ji2tab/OpenCCVoice/CCVoice_2_24f/NOTES_FOR_UPGRADE.md

# アップグレードガイド — OpenCCVoice

--------------------------------------------------------------------

## v2.24 → v2.24f アップグレード

**スケッチの差し替えのみで完了します。**

- `V`（バージョン確認）と `Z`（ソフトウェアリセット）コマンドの追加のみです。
- EEPROM CONFIG_VERSION = 6（変更なし）。`F` コマンド不要。

### 追加コマンド

| コマンド | 機能 | EEPROM | MCU |
|---|---|---|-----|
| `V` | バージョン文字列 + EEPROM_VER を表示 | 変化なし | 動き続ける |
| `Z` | WDTによるソフトウェアリセット | 変化なし | 再起動 |

> **注意**：PTT 出力中に `Z` を実行すると WDT ハードリセットにより PTT が即解放されます。

### 手順
1. ZIP を展開し、`CCVoice_2_24f` フォルダごと Arduino のスケッチフォルダに配置
2. Arduino IDE で `CCVoice_2_24f.ino` を開く
   （`ccvoice_log.h` / `ccvoice_config.h` は同フォルダに必須）
3. マイコンボードに書き込む

--------------------------------------------------------------------

## v2.23 → v2.24 アップグレード

**スケッチの差し替えのみで完了します。**

- 内部アーキテクチャの最適化のみで、機能・設定の変更はありません。
- EEPROM CONFIG_VERSION = 6（変更なし）。`F` コマンド不要。

### 手順
1. ZIP を展開し、`CCVoice_2_24` フォルダごと Arduino のスケッチフォルダに配置
2. Arduino IDE で `CCVoice_2_24.ino` を開く
   （`ccvoice_log.h` / `ccvoice_config.h` は同フォルダに必須）
3. マイコンボードに書き込む

--------------------------------------------------------------------

## v2.10 / v2.21（以前） → v2.23 アップグレード

**スケッチの差し替えのみで完了します。**

- v2.20 / v2.21 / v2.22 は廃止。**v2.23 をご使用ください。**
- EEPROM CONFIG_VERSION = 6（変更なし）。`F` コマンド不要。
- v2.10 からのアップグレードも同手順で完了します（自動マイグレーション）。

### 手順
1. ZIP を展開し、`CCVoice_2_23` フォルダごと Arduino のスケッチフォルダに配置
2. Arduino IDE で `CCVoice_2_23.ino` を開く
   （`ccvoice_log.h` / `ccvoice_config.h` は同フォルダに必須）
3. 書き込む

--------------------------------------------------------------------

## v2.20 → v2.21（廃止バージョン間 / 記録のみ）

> ⚠️ v2.20 / v2.21 は廃止です。v2.23 をご使用ください。

- EEPROM CONFIG_VERSION = 6（変更なし）。
- AT24C32 が接続されていれば自動的にログ記録を開始。

--------------------------------------------------------------------

## v2.10 → v2.20（廃止バージョン間 / 記録のみ）

> ⚠️ v2.20 は廃止です。v2.23 をご使用ください。

- EEPROM CONFIG_VERSION: 5 → 6 に自動マイグレーション。
- 初回起動時に `saveTimestamp=0` で自動補完。既存設定は引き継ぎ。
- AT24C32 接続時は自動的に外部 EEPROM へ設定を移行。

--------------------------------------------------------------------

## v2.01 → v2.10 アップグレード

**スケッチの差し替えのみで完了します。**

- EEPROM CONFIG_VERSION: 4 → 5 に自動マイグレーション。
- 初回起動時に `rtcAlignOn=1`（ON）で自動補完。
- DS3231 未接続でも millis() 相対動作で従来通り動作。

--------------------------------------------------------------------

## v1.73e → v2.01 アップグレード（Ver.4 → Ver.5 基板移行）

> ⚠️ **基板の交換を伴うアップグレードです。ピンアサインが変わります。**

- Ver.4 基板に v2.01以降を書き込んではいけません。
- EEPROM レイアウトは v1.73e と同一（config.ver = 4）。
  設定は引き継がれますが、ピン変更のため動作確認を必ず行ってください。

--------------------------------------------------------------------

## EEPROM CONFIG_VERSION 変更履歴

| ver | 対応ファームウェア | 追加フィールド |
|-----|---|---|
| 4 | v1.73d〜v2.01 | periodQuietMs |
| 5 | v2.10 | rtcAlignOn |
| 6 | v2.20〜v2.24f | saveTimestamp |

--------------------------------------------------------------------
End of NOTES_FOR_UPGRADE
