ji2tab/OpenCCVoice/CCVoice_1_80h/opencccvoice_180g_timing_part2.pdf

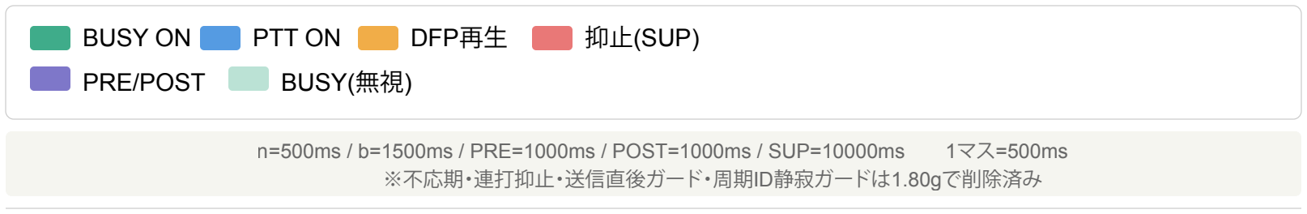
[picture p2: figure]
BUSY ON; PTT ON; DFP再生; 抑止(SUP); PRE/POST; BUSY(無視); ※不応期・連打抑止・送信直後ガード・周期ID静寂ガードは1.80gで削除済み

n=500ms / b=1500ms / PRE=1000ms / POST=1000ms / SUP=10000ms　　1マス=500ms

## ⑤ 周期ID送出（IDLE かつ BUSY OFF）

定時到来 → IDLE・非抑止・BUSY OFFなら即送出（002.mp3）

0 | 2s | 3s | 4s | 4.5s | 5.5s

### ↑定時到来(1s)→即送出

### BUSY

### PTT

DFP再生 | PRE 1s | 002.mp3 | POST 1s

# ⑥ 周期IDスキップ（BUSY中 / SUP中）

## BUSY中・SUP中・PTT中に定時到来 → スキップ（次の定時まで何もしない）

0 | 1s | 3s | 4s | 4.5s | 5.5s | 6.5s

### BUSY

### PTT

periodicDue | crossed=false → スキップのみ（保持しない）
| | ↑定時到来(1.5s,BUSY中)→スキップ

### PTT発生なし（BUSY中のためスキップ）

v1.73f1: periodicDue=true保持 → BUSY OFF後k秒静寂 → 送出

### v1.80g: 完全スキップ → 次の定時まで何もしない

# ⑦ 送信直後ガード（SUPでブロック）

## POST終了→SUP開始（起点A）→残留BUSYはSUP中なのでスキップ

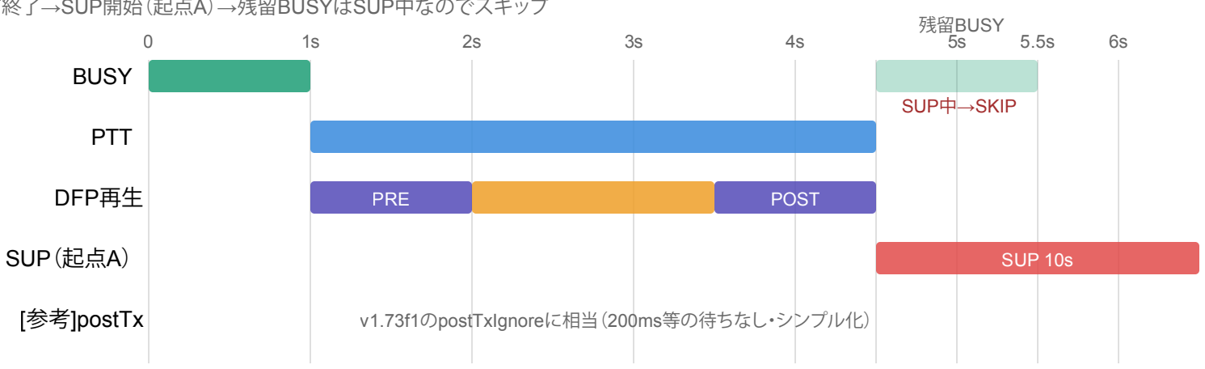
[picture p3: figure]
BUSY; 残留BUSY; SUP中→SKIP; PTT; DFP再生; PRE; POST; SUP（起点A）; SUP 10s; [参考]postTx; v1.73f1のpostTxIgnoreに相当（200ms等の待ちなし・シンプル化）

### POST終了→SUP開始（起点A）で残留BUSYを自動ブロック
