ji2tab/OpenCCVoice/CCVoice_1_73f/OpenCCVoice_TimingChart.pdf

信号名 | 補足 | 0s | 2s | 4s | 6s | 8s | 10s | 12s | 14s | 16s | 18s | 20s | 22s | 24s | 26s | 28s | 30s | 32s | 34s | 36s

受信BU受信信号 D6/A0

カーチャ受信長評価

長話抑止LONG_SUP 10s

連打検出BURST_WIN 10s

連打抑止BURST_SUP 10s

PTT出力D5 HIGH=送信 DFPlay D7 BUSY 再生 送信直後BUSY安定待ち 不応期 送信後抑TX_SUP 3s 周期タイperiodicDue | REFRAC 3s

静寂ガーQUIET k#### ms

① | 短発受信
② | PTT先行ON（無音）
③ | ID音声送出
④ | PTT後行保持（無音）
⑤ | 不応期
⑥ | 送信後抑止
⑦ | 長話受信
⑧ | 長話抑止
⑨ | 連打1回目
⑩ | 連打2回目→抑止
⑪ | 連打検出窓
⑫ | 連打抑止
⑬ | スケルチテール
⑭ | 瞬間BUSY揺れ
⑮ | 送信直後ガード
⑯ | 通話中（定時到来）
⑰ | 通話再来→再延期
⑱ | 周期ID定時到来
⑲ | 静寂待ち（延期）
⑳ | 静寂条件成立

静寂待ち中に再度受信。静寂カウントをリセットして再度待機。

設定した周期（p##分）が経過しperiodicDue=trueになった状態。送出条件が整うまで待機し続け る。
BUSY OFFになったが⑯⑰の通話再来により静寂条件（ QUIET=2000ms連続OFF）を満たせず延 期。

BUSY OFFから2秒間静寂が続き送出条件成立。周期IDを送出する。

PTT解放直後にA0/D6に残留するBUSY信号。実際には送信していないが信号が残っている状態。

スケルチが完全に閉じる前の瞬間的なBUSY信号の揺れ。誤って短発IDを送出させる原因になる。

PTT解放後にpostTxIgnore=trueをセット。BUSYが200ms連続OFFになるまで次のトリガーを受け 付けない。⑬⑭のような残留・揺れによる誤発火を防ぐ。

⑤ 周期ID 静寂ガード

周期IDの定時が来ているが、相手局が通話中のため静寂条件を満たさず送出を延期。

短発1回目を検出。連打検出窓（10秒）の計測を開始。

10秒窓内に短発2回目を検出。連打と判定し、ID送出後に連打抑止を開始。

短発1回目から10秒間の検出窓。この窓内に短発が2回以上来ると連打と判定。

連打2回目検出後10秒間、以降の短発IDを抑止。頻繁な呼び出しによる連続送出を防止。

④ 送信直後ガード

PTT解放後3秒間、受信BUSY信号を無視する。自局の送信によるエコーバックや残響を誤検知しな いための保護。

② 長話抑止

受信継続時間が5.2秒でMAX(3900ms)を超えた。長話と判定されID送出は行われない。

長話終了後10秒間、短発IDの送出を抑止。通話の切れ目に誤って送出しないための保護。

③ 連打抑止

カーチャンクを1.4秒検出。MIN(500ms)≤継続時間<MAX(3900ms)の範囲に収まるため、短発と判 定。
カーチャンク検出によりPTTをONにし、1秒間無音のまま電波を出す。相手局に送信開始を知らせ る先行時間。

DFPlayerがトラック001（ID音声）を再生。PTTはONのまま保持。

ID再生終了後、PTTを1秒間保持してから解放。尻切れを防ぐ後行時間。

ID送出開始から3秒間、次の短発IDトリガーを受け付けない。連続送出を防止。

⑱ 定時到来

⑲ 静寂待ち→延期 | ⑳ QUIET 2s OK

■ 各番号の動作解説
① 短発 → ID送出
true | ⑮ BUSY安定待ち
⑤ REFRAC 3s | REFRAC 3s
⑥ TX_SUP 3s | TX_SUP 3s | TX_SUP 3s

002送出

001 ID | 001 | 001 | 002

⑧ 抑止 10s

⑪ BURST_WIN 10s

⑫ 連打抑止 10s

② PRE 1s | ③ ID再生 | ④ POST 1s | PRE | 再生 | POST | PRE | 再生 | POST
⑭ | ⑯ 通話中 | ⑰
MIN≤dur<MAX | 長話判定 | 短発① | 短発②→抑止
① 短発 1.4s | ⑦ 長話 5.2s | ⑨ 短発① | ⑩ 短発② | 残留テー

## OpenCCVoice v1.73f タイムチャート（1セル = 200ms）

① 短発 → ID送出 | ② 長話抑止 | ③ 連打抑止 | ④ 送信直後ガード | ⑤ 周期ID 静寂ガード
