ji2tab/OpenCCVoice/old_firmware/CCVoice_1_73a/SPECIFICATION.md

========================================================================
【仕様書（技術者向け）】
========================================================================

1. 基本情報
- 名称     : OpenCCVoice Guidance Controller
- バージョン: v1.73b-Unified-Safe
- MCU      : Arduino Nano（ATmega328P, 5V）
- 依存     : Arduino.h / SoftwareSerial.h / EEPROM.h
- DFPlayer : BUSY監視（D7=LOW 再生中）、9600bps 制御（固定）

========================================================================
2. 機能仕様（Functional）
========================================================================

(1) 短発受信の自動ID送出
  - D6 または A0 の受信継続時間 dur が
      BUSY_MIN_MS ≤ dur < BUSY_MAX_MS のとき、
      トラック1（001）を送出。
  - D6 BUSY は極性切替可能（g0/g1）。
      g0: LOW=受信 / g1: HIGH=受信。
  - DFPlayer BUSY（D7）の戻りは「HIGH連続40ms」で再生完了と判定。
  - PTT シーケンス：
      PRE=1000ms → 再生 → POST=1000ms。

(2) 抑止（長話・バースト・送信後）
  - 長話抑止      ：dur ≥ BUSY_MAX_MS → LONG_SUP_MS=10s。
  - バースト抑止  ：10秒窓内で2回以上の短発 → BURST_SUP_MS=10s。
  - 送信後抑止    ：t1有効時は TX後 TX_SUP_MS(ms) の受信を無視。

(3) AUTO（m2）
  - AUTO_WINDOW（分）中に
      D6エッジ数 / A0イベント数を計測し優位側へ自動固定。
  - 固定後 autoLocked=true、EEPROM 保存（再起動後も反映）。
  - AUTO固定時は D13 LED を高速点滅（約3秒）で通知。

(4) 周期ID
  - PERIOD_MS ごとにトラック2/3を交互送出。
  - IDLE時のみ動作。
  - 絶対時刻基準で等間隔実行（起動からの経過時間ベース）。

(5) EEPROM 永続化
  - m / n / b / i / p / r / L / G / a / w / s / t / d / g
    すべての設定変更で即保存。
  - 起動時は EEPROM からロード。magic 不一致時は applyDefaults()。

(6) LED可視化 / D2ミラー出力
  - 使用側LED（D6系=D4, A0系=D12）は実際のBUSYを表示。
  - 未使用側LEDはゆっくり点滅（待機表示）。
  - 抑止LED（D13）は抑止・バースト・AUTO固定通知を表現。
  - D2：DFPlayer BUSY ミラー出力（反転）
      再生中=HIGH / 停止中=LOW。

(7) フェイルセーフ（PTT張り付き防止）
  - PLAYING 以降、DFPlayer BUSY が戻らない場合、
      設定 d####（既定20000ms = 20秒）で強制 PTT OFF。
  - d0 で無効化可能（無効時は PLAYING 内で判定スキップ）。

========================================================================
3. 非機能仕様（Non-Functional）
========================================================================
- 応答性：D6 デバウンス 5ms。
- 安定性：D7 BUSY の HIGH確定に 40ms の安定時間。
- PTT 最低ONガードを搭載し、誤送信防止。
- 可搬性：Arduino IDE 1.8.x / 2.x。
- 保守性：printSummary() による状態可視化、ログレベル制御。
- 安全性：フェイルセーフ（既定20秒、d####で可変、d0で無効）。

========================================================================
4. インタフェース仕様（I/O / 配線）
========================================================================
- D2  : DFP BUSY ミラー出力（反転）… 再生中=HIGH / 停止中=LOW
- D3  : テストSW（INPUT_PULLUP, 1〜3クリックでトラック1〜3）
- D4  : D6 系 LED（デジタル受信表示）
- D5  : PTT 出力（HIGH=送信）
- D6  : TM BUSY入力（g0/g1 により極性可変）
        g0 = LOW=受信（アクティブLOW）
        g1 = HIGH=受信（アクティブHIGH）
- D7  : DFPlayer BUSY入力（LOW=再生中）
- D10 : Arduino RX（← DFPlayer TX）
- D11 : Arduino TX（→ DFPlayer RX）
- D12 : A0 系 LED（アナログ受信表示）
- D13 : 抑止/AUTO LED（抑止・短発窓・AUTO固定の可視化）
- A0  : アナログ入力（0..1023、ヒステリシス L/G + 保持 a）

========================================================================
5. 既定値（Factory Defaults）
========================================================================
- BUSY_INPUT_SOURCE           = D6
- BUSY_MIN_MS                 = 500
- BUSY_MAX_MS                 = 3900   (= LONG_TALK_MS)
- IDLE_MIN_MS                 = 200
- PERIOD_MS                   = 30 min
- TX_SUP_MS                   = 3000
- SUPPRESSORS_ENABLED         = true
- TX_AFTER_SUPPRESS_ENABLED   = true
- A0_LOW_TH                   = 300
- A0_HIGH_TH                  = 700
- A0_HOLD                     = 800
- AUTO_WINDOW                 = 30 min
- D6 デバウンス               = 5ms
- DFP_TIMEOUT_MS              = 20000ms（d####で変更可 / d0=無効）
- TM_BUSY_ACTIVE_HIGH         = true（=HIGHがBUSY）  
  ※ g0/g1 で変更可能（g0=LOW=BUSY, g1=HIGH=BUSY）

========================================================================
6. コマンド仕様（完全）
========================================================================
- m0 / m1 / m2         … モード切替（D6固定 / A0固定 / AUTO）
- n####                … 最小受信時間（ms）
- b####                … 最大受信時間（ms）
- i####                … 直前アイドル最小時間（ms）
- s0 / s1              … 抑止 OFF / ON
- t0 / t1              … 送信後抑止 OFF / ON
- r####                … 送信後抑止（ms）
- p##                  … 周期ID（分, 0=停止）
- w##                  … AUTO 観測窓（分）
- L### / G### / a####  … A0閾値LOW / HIGH / 保持(ms)
- d####                … DFPフェイルセーフ（ms, 0=無効）
- g0 / g1              … TM BUSY 極性設定（0:LOW=BUSY, 1:HIGH=BUSY）
- q                    … 現在値の要約表示（DFP_TIMEOUT / BUSY極性含む）
- H                    … 汎用プリセット（s0 / t0 / b3900）
- x / r                … 停止（Safe Stop）/ 再開（停止時のみ有効）
- F                    … Factory Reset（初期化+EEPROM保存）
- 0 / 1 / 2 / 3        … ログレベル（NONE / ERR / INF / DBG）

========================================================================
7. 振る舞い仕様（状態遷移 / BUSY判定）
========================================================================
【受信長判定】
- dur <  MIN                → 無効
- MIN ≤ dur < MAX          → 短発（ID 送出候補）
- dur ≥ MAX                → 長話抑止（LONG_SUP_MS）

【短発連続】
- 10s窓で2回以上 → BURST_SUP_MS=10s 抑止

【送信後抑止】
- t1 & r#### により TX後の BUSY を無視

【フェイルセーフ】
- PLAYING → (now - playingEnterAt ≥ d####) → 強制PTT OFF
- d0 の場合はチェックをスキップ

【PTT状態遷移】
- IDLE → PTT_ON_WAIT（PRE）
       → PLAYING（D7 LOW→HIGH確定）
       → PTT_OFF_WAIT（POST）
       → IDLE

========================================================================
8. 制約
========================================================================
- D6 デバウンス 5ms（固定）
- EEPROM 書込みは「値変更時のみ」
- SRAM 制約：ATmega328P の 2KB 内で運用

========================================================================
9. 試験（例）
========================================================================
- D6固定（m0）  
  600ms BUSY → ID送出  
  4000ms BUSY → 長話抑止  
- AUTO：m2 → w1分 → 観測満了 → [AUTO-FIXED] & D13高速点滅  
- 送信後抑止：t1 / r3000 → 自局送出後3s無視  
- フェイルセーフ：d20000 → BUSY戻らず20秒経過で強制OFF  
  d0 → フェイルセーフ無効  
- TM BUSY極性  
  g0=LOW=BUSY（アクティブLOW）  
  g1=HIGH=BUSY（アクティブHIGH）

========================================================================
10. リスク
========================================================================
- DFPlayer BUSY の個体差（LOW/HIGH の応答速度差）
- 外部回路のプルアップ不足による D6/A0 不安定
- A0/D6 の同時配線は禁止（AUTO は判定のみであり、配線は常に片側）
- 無線機 BUSY の極性仕様を誤ると短発/長話判定が乱れるため g0/g1 を適切に設定

========================================================================
11. 変更履歴
========================================================================
- 詳細は CHANGELOG.md を参照

========================================================================
