ji2tab/OpenCCVoice/circuit/配線図Ver4-4.pdf

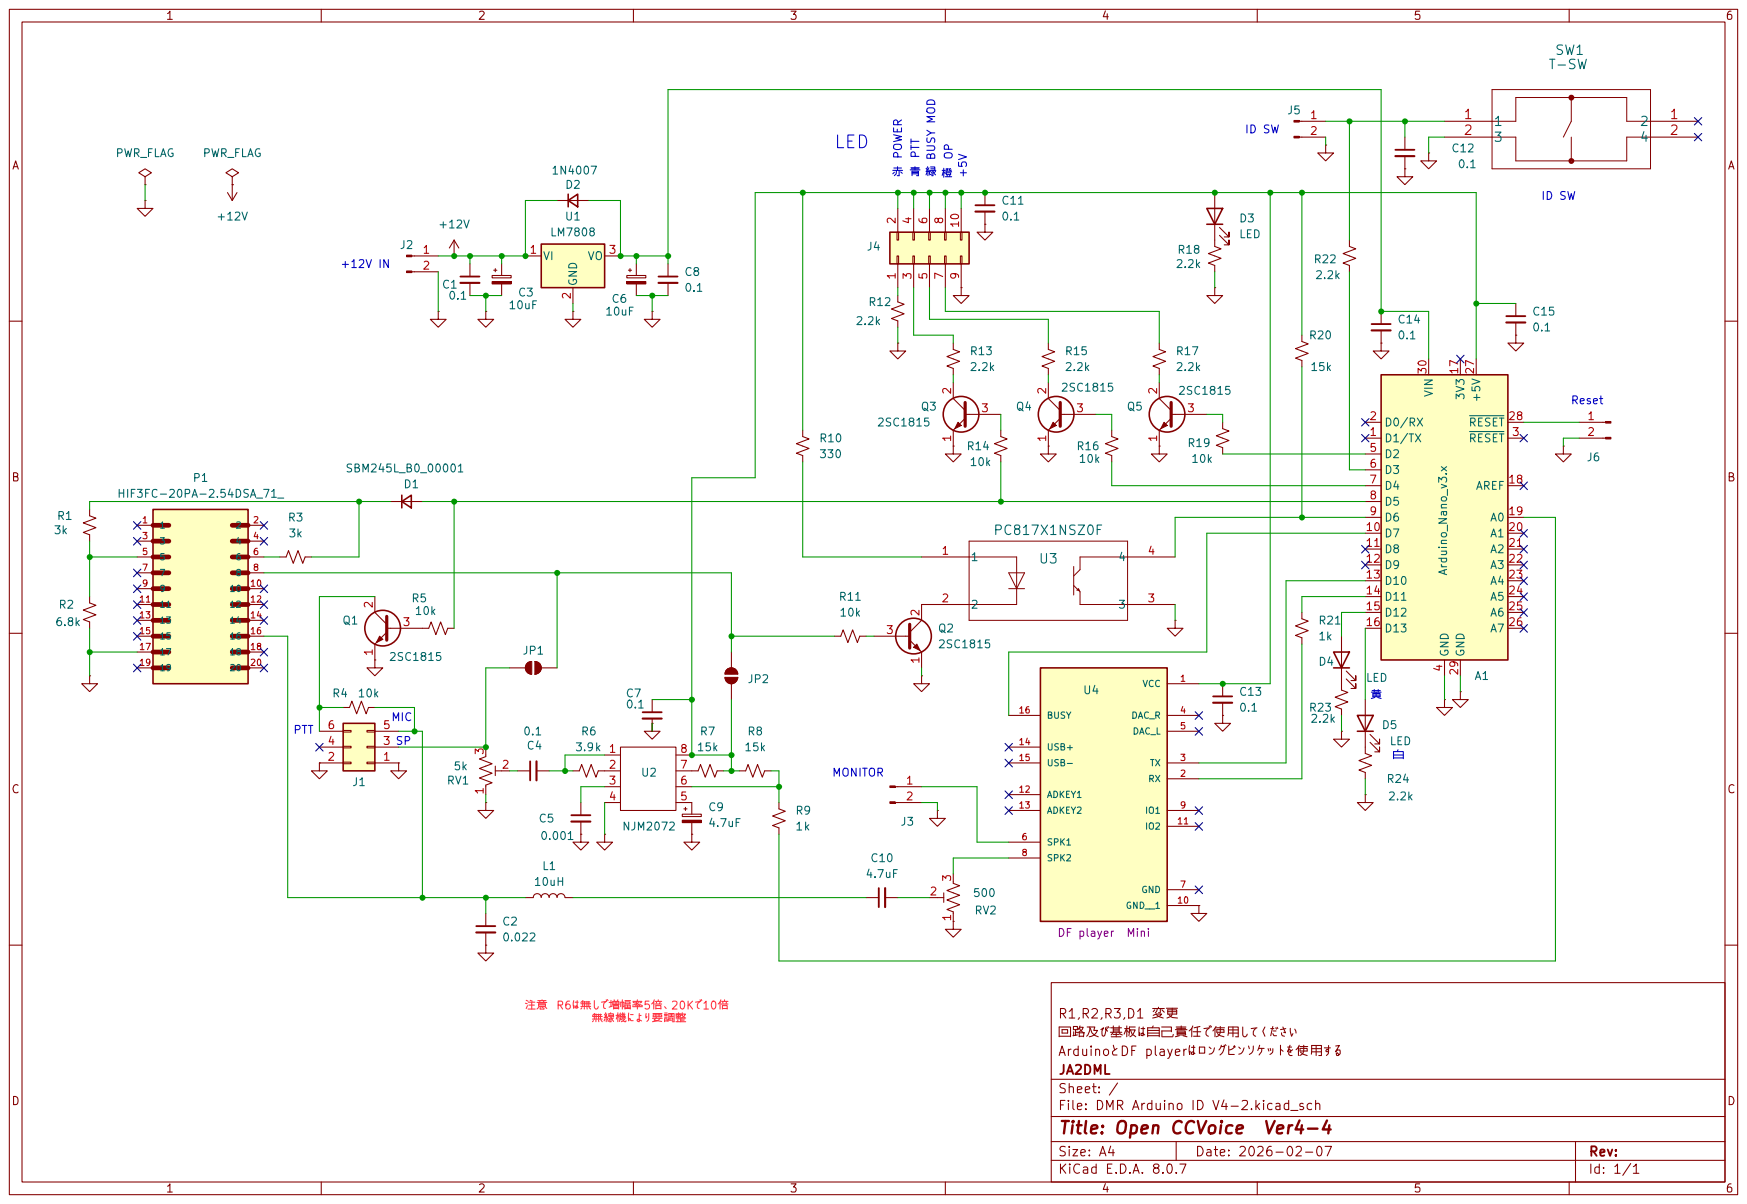
[picture p13: page 1]
