ji2tab/OpenCCVoice/DMR Arduino ID V4-2/配線図Ver4-3.pdf

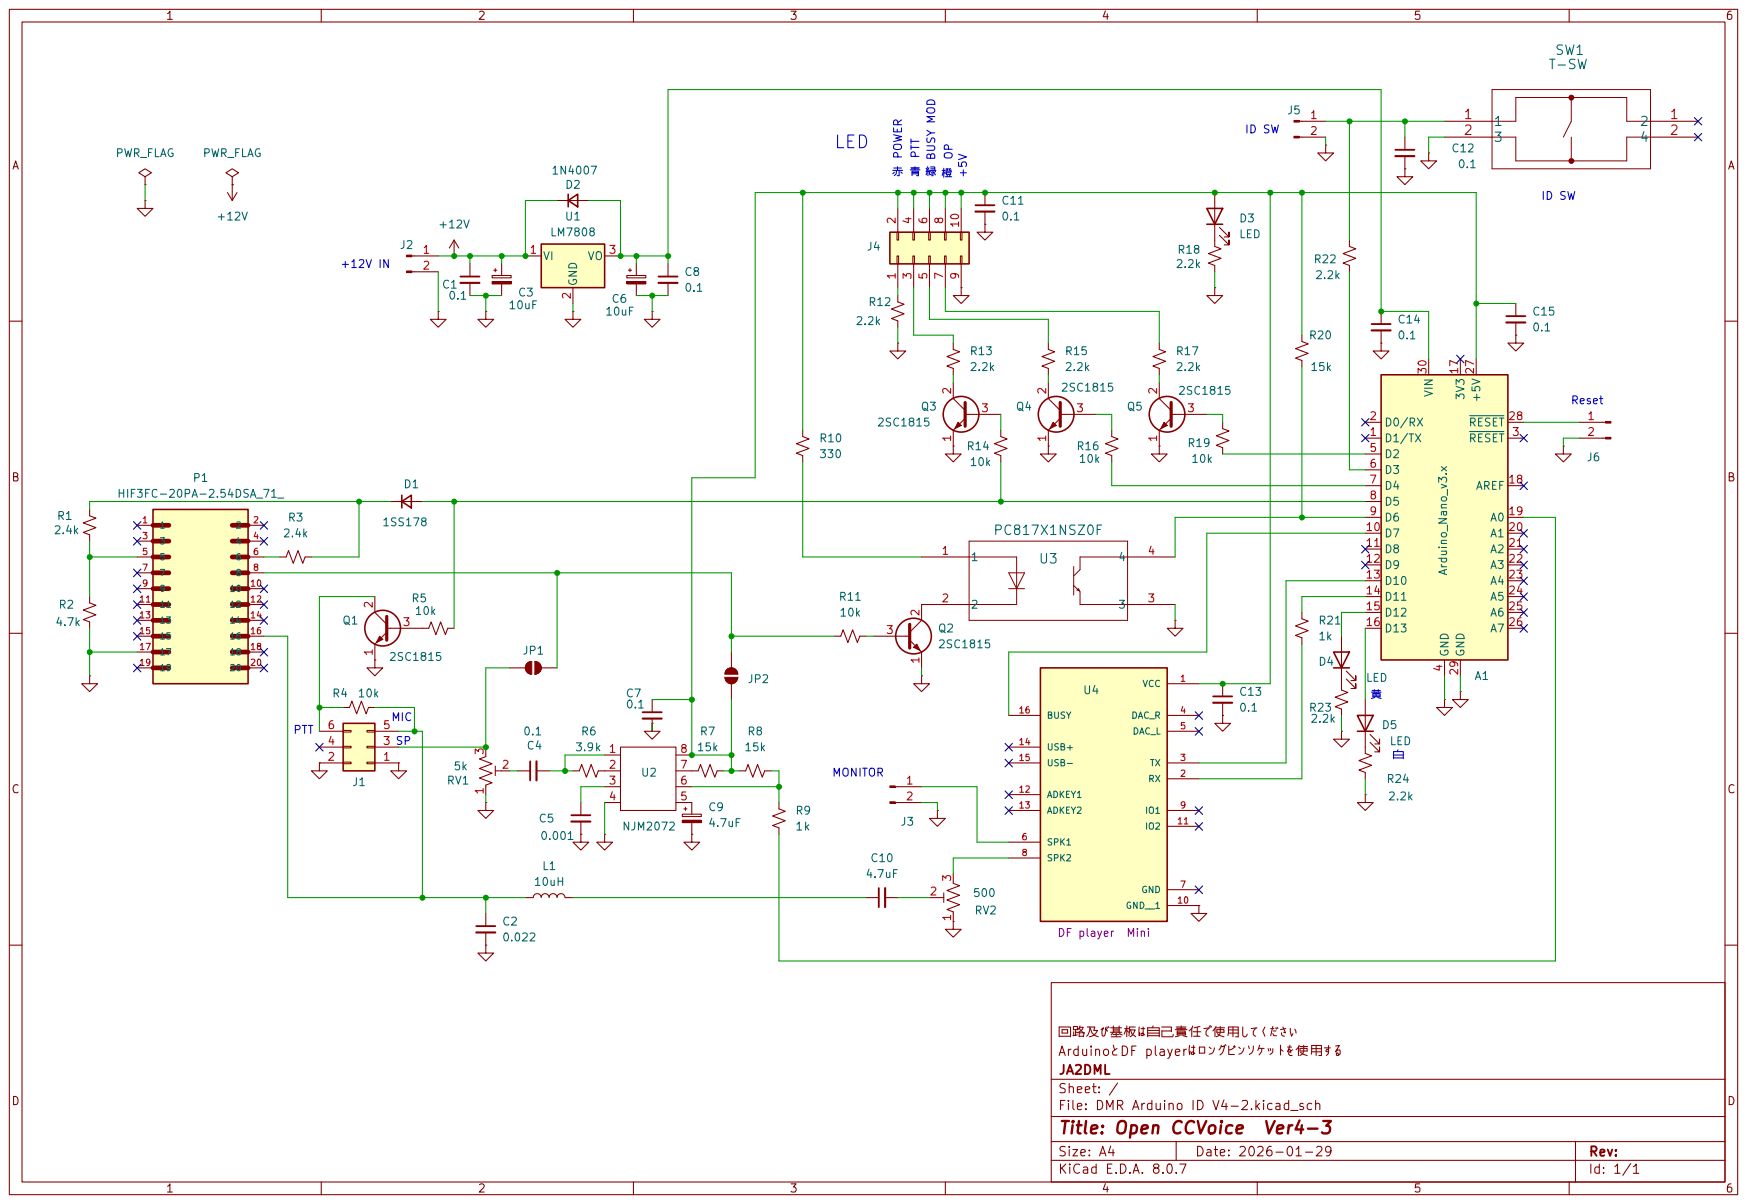
[picture p14: page 1]
