ji2tab/OpenCCVoice/CCVoice_2_10/Schematic_Ver5.pdf

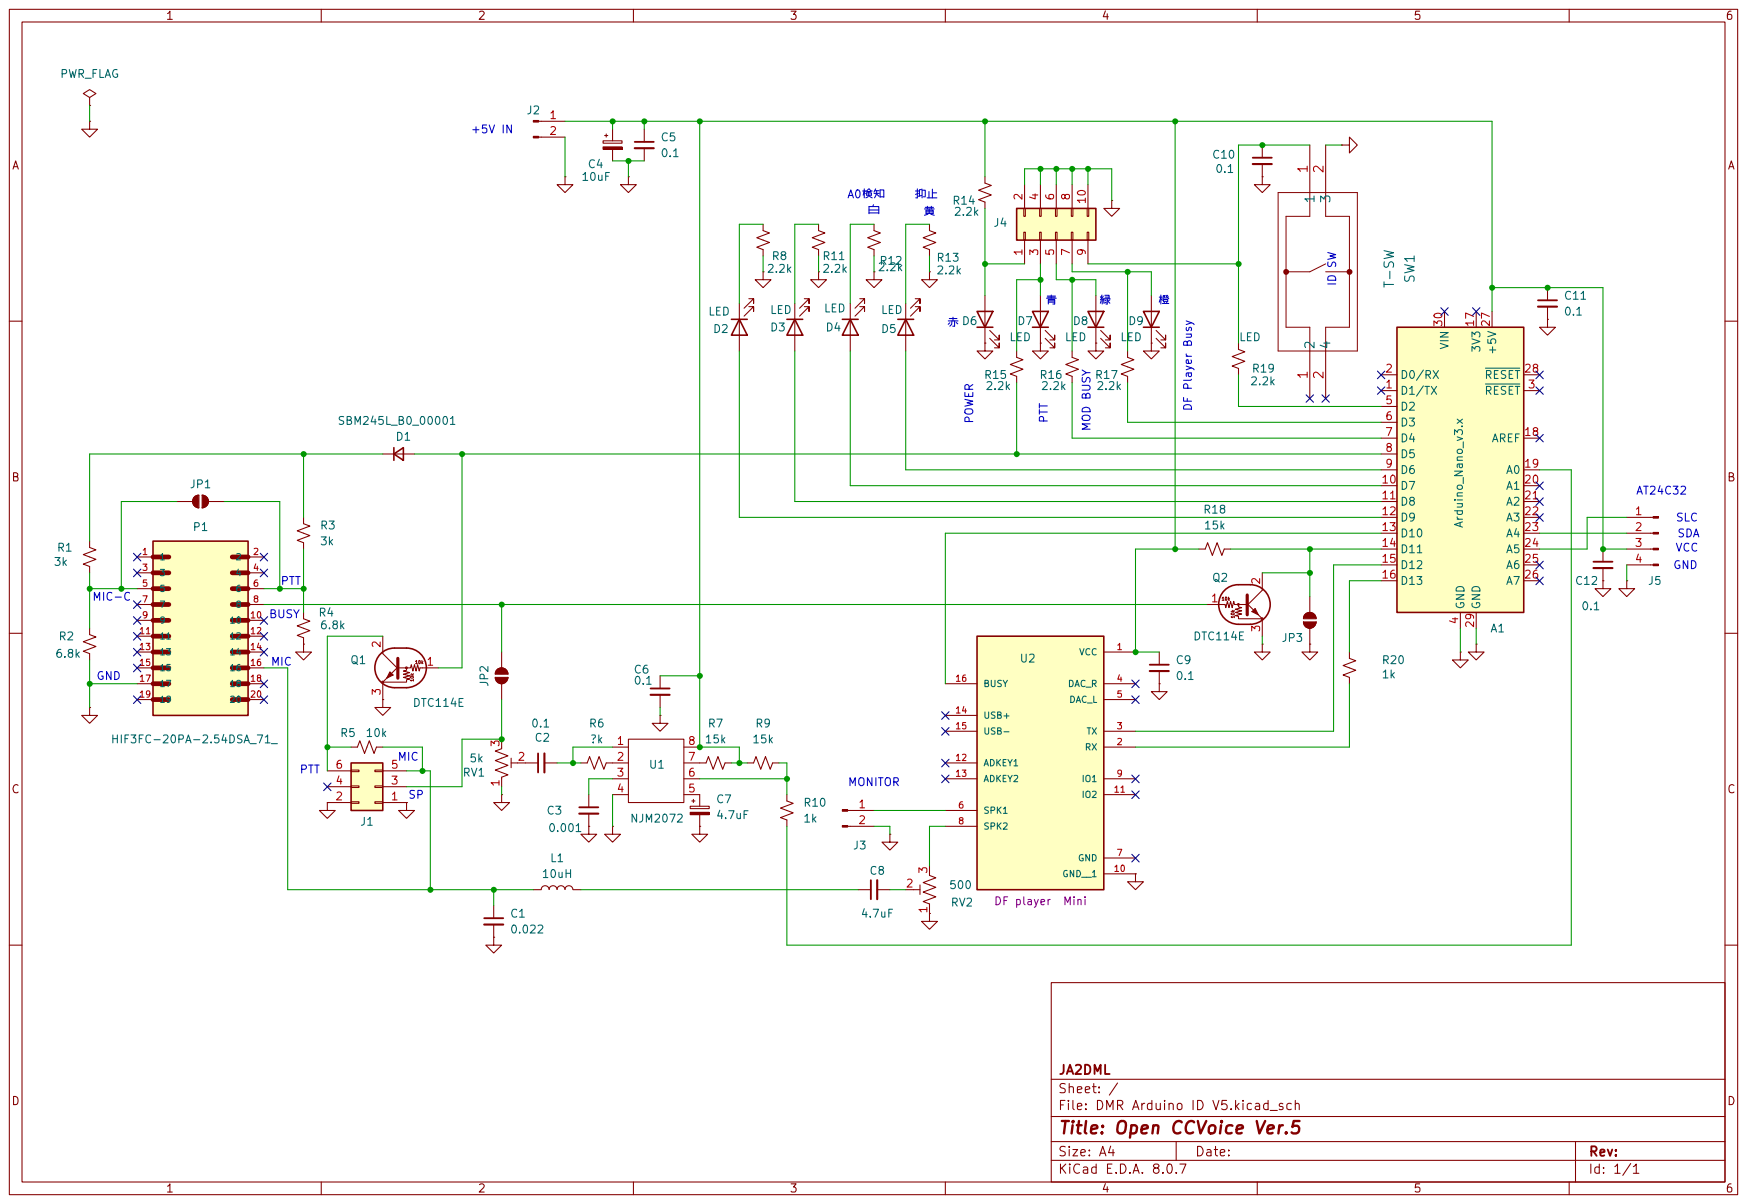
[picture p15: page 1]
