ji2tab/OpenCCVoice/CCVoice_2_10/PCB_Layout_Ver5.pdf

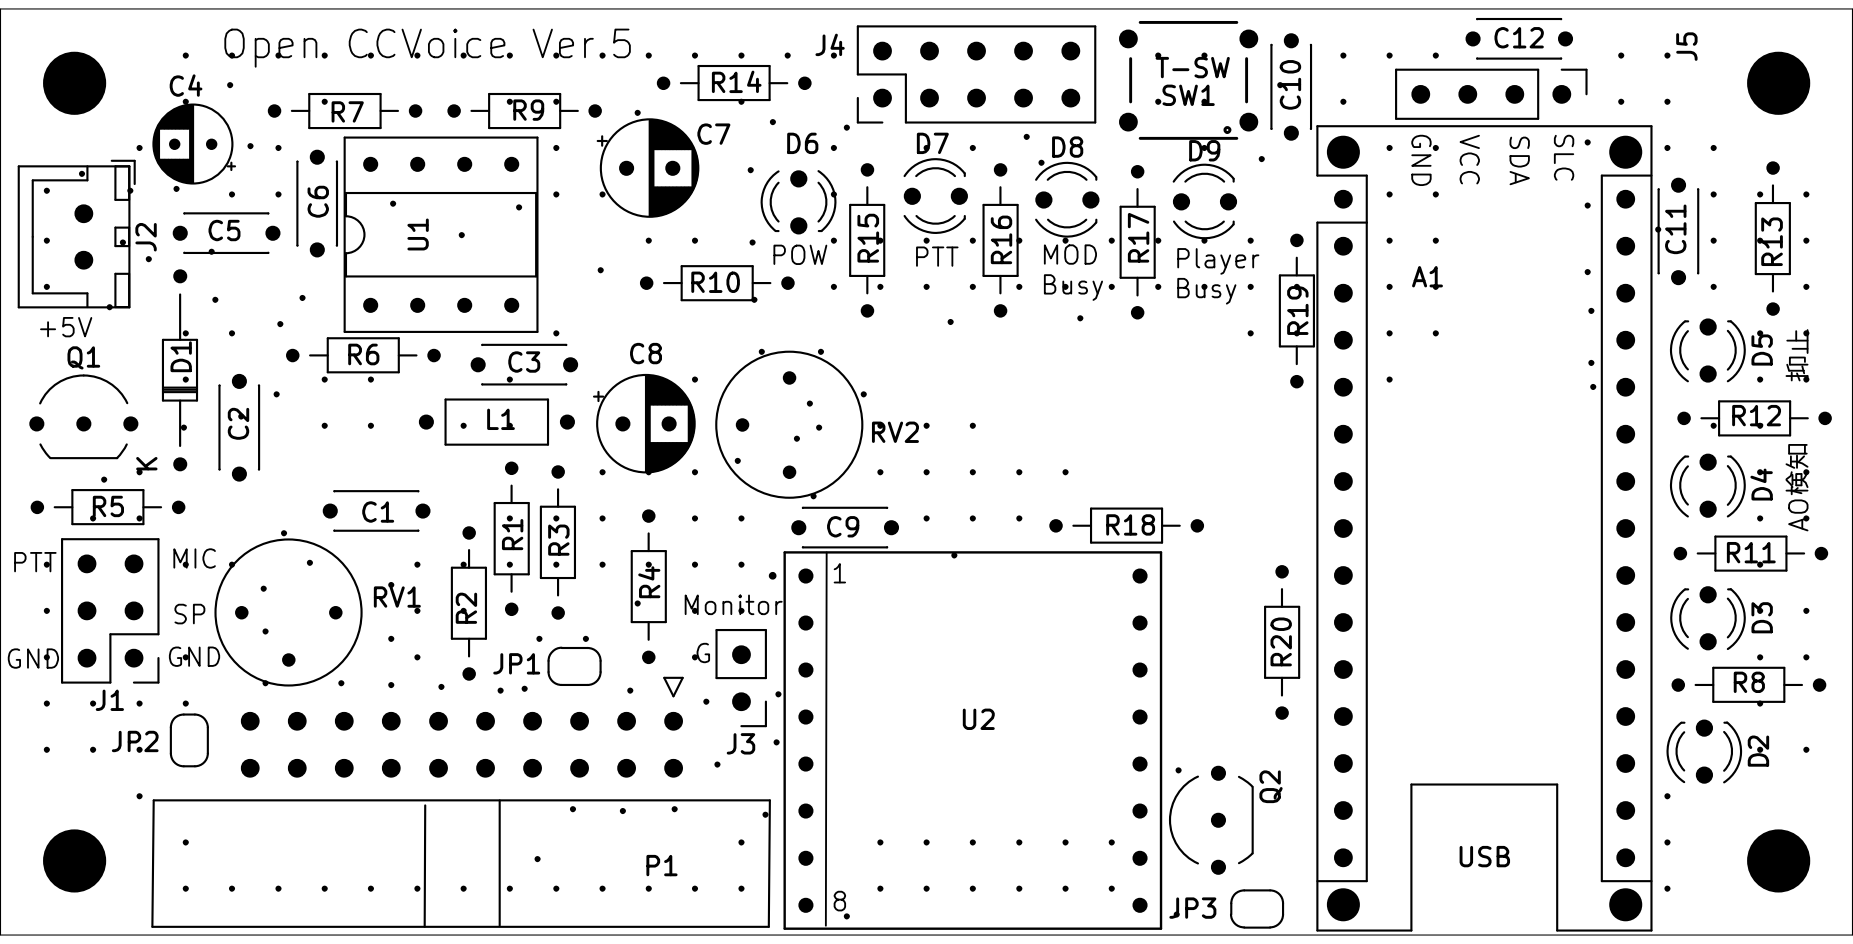
[picture p16: page 1]
